Centre-Alt-Rendiment-Esportiu/att/TableTennisTracking7/data/training.gif

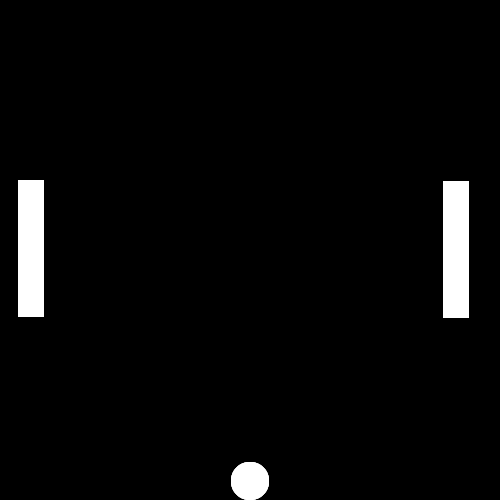
TableTennisTracking7/data/training.gif
